PubInv/RCICS/designs/september-2026/CAD/stl/scaled to 3dprint/cover-coverExtrudedCutout001_scaled.stl

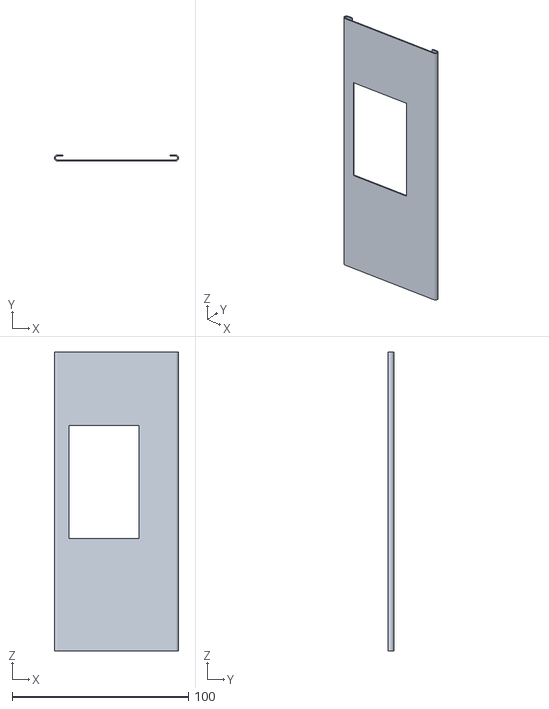
[picture p15: CAD file, 2026-09-14]
designs/september-2026/CAD/stl/scaled to 3dprint/cover-coverExtrudedCutout001_scaled.stl
70.6 x 3.40 x 169.8
