PubInv/RCICS/designs/september-2026/CAD/PARTS/R_frame.FCStd

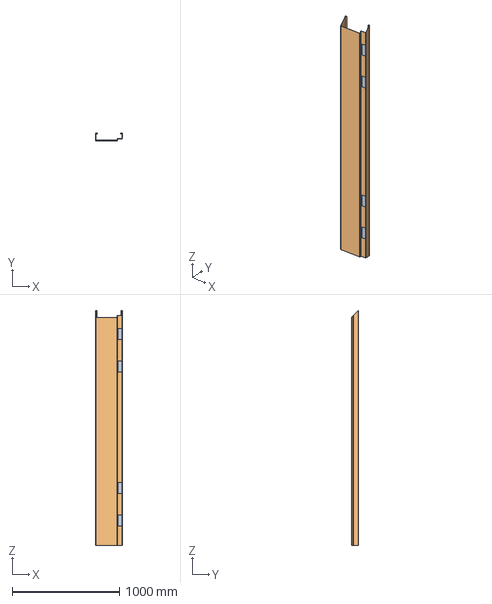
[picture p16: CAD file, 2026-09-14]
designs/september-2026/CAD/PARTS/R_frame.FCStd
250.0 x 66.0 x 2187.5 mm
ExtrudedCutout001
ExtrudedCutout002
