PubInv/RCICS/designs/september-2026/CAD/PARTS/scaled to 3dprint/Lshape1_scaled.FCStd

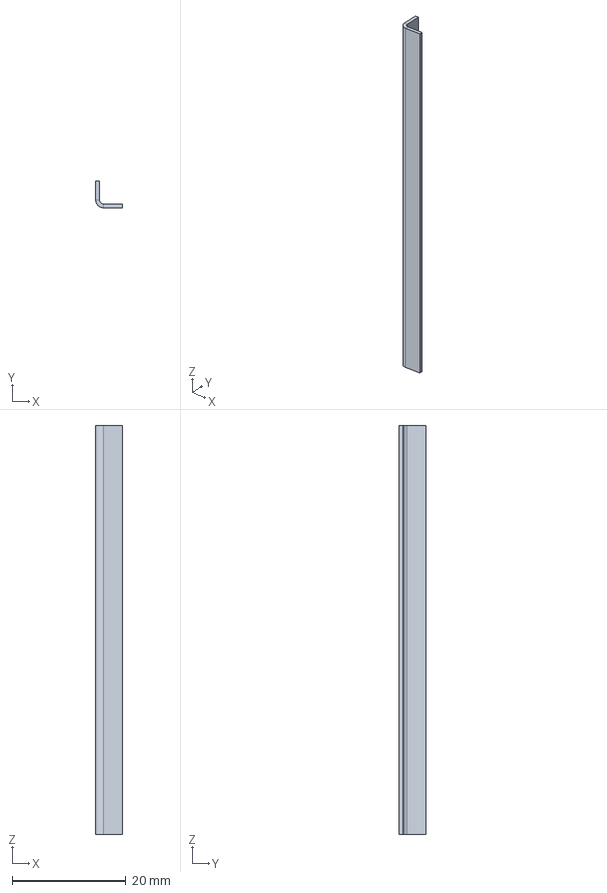
[picture p17: CAD file, 2026-09-14]
designs/september-2026/CAD/PARTS/scaled to 3dprint/Lshape1_scaled.FCStd
4.70 x 4.70 x 72.0 mm
