PubInv/RCICS/designs/september-2026/CAD/stl/Frame.stl

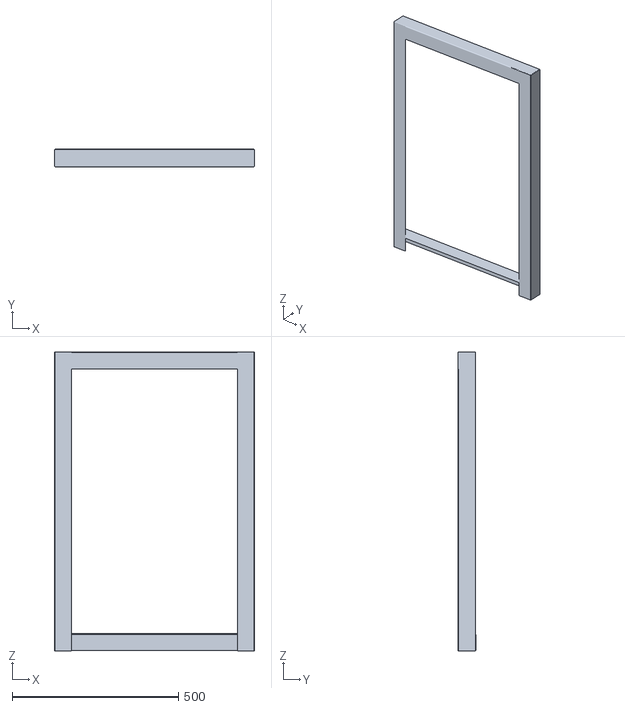
[picture p18: CAD file, 2026-09-14]
designs/september-2026/CAD/stl/Frame.stl
603.0 x 53.0 x 900.5
