PubInv/RCICS/designs/september-2026/CAD/PARTS/Lshape1.FCStd

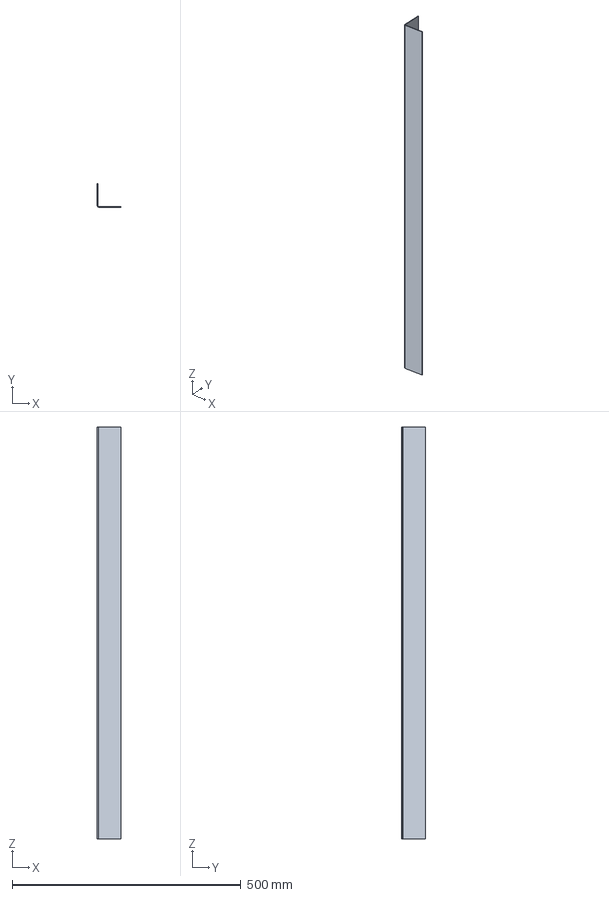
[picture p19: CAD file, 2026-09-14]
designs/september-2026/CAD/PARTS/Lshape1.FCStd
51.5 x 51.5 x 900.0 mm
