PubInv/RCICS/designs/september-2026/CAD/PARTS/T_frame.FCStd

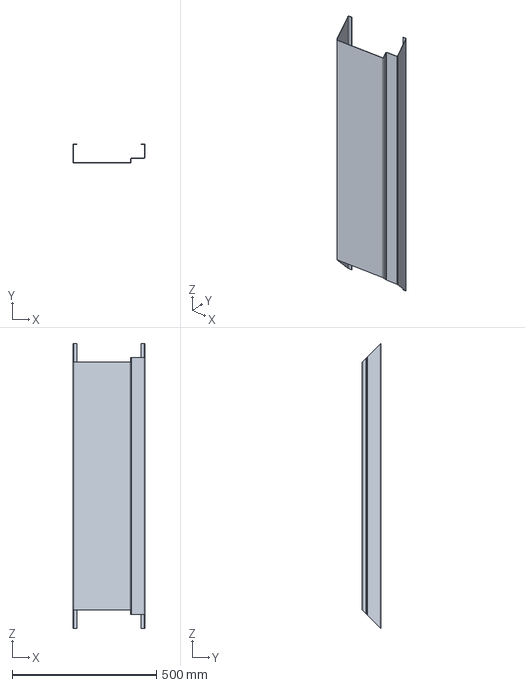
[picture p20: CAD file, 2026-09-14]
designs/september-2026/CAD/PARTS/T_frame.FCStd
250.0 x 66.0 x 987.0 mm
