PubInv/RCICS/designs/september-2026/CAD/PARTS/Lshape2.FCStd

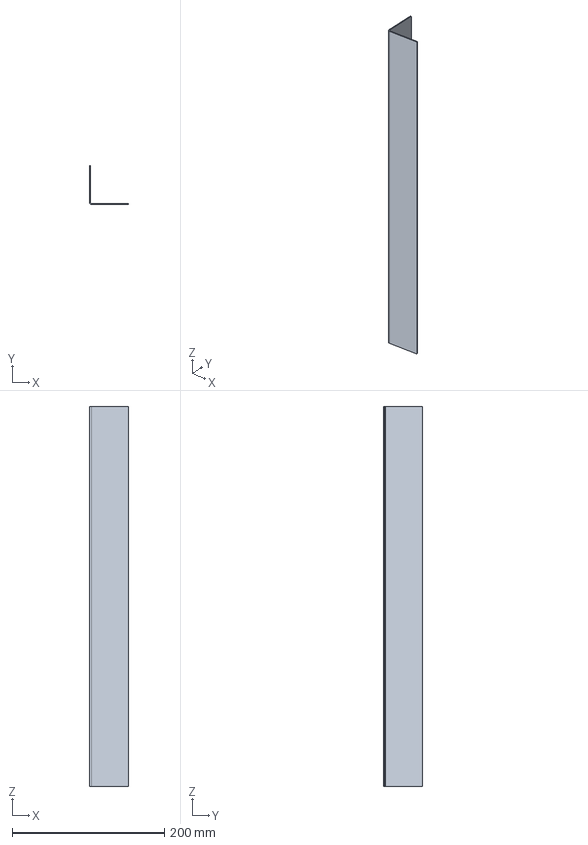
[picture p21: CAD file, 2026-09-14]
designs/september-2026/CAD/PARTS/Lshape2.FCStd
51.5 x 51.5 x 500.0 mm
